tuofeichen/ME433-Advanced-Mechatronics/HW1/Clean 3.3 w: cap.png

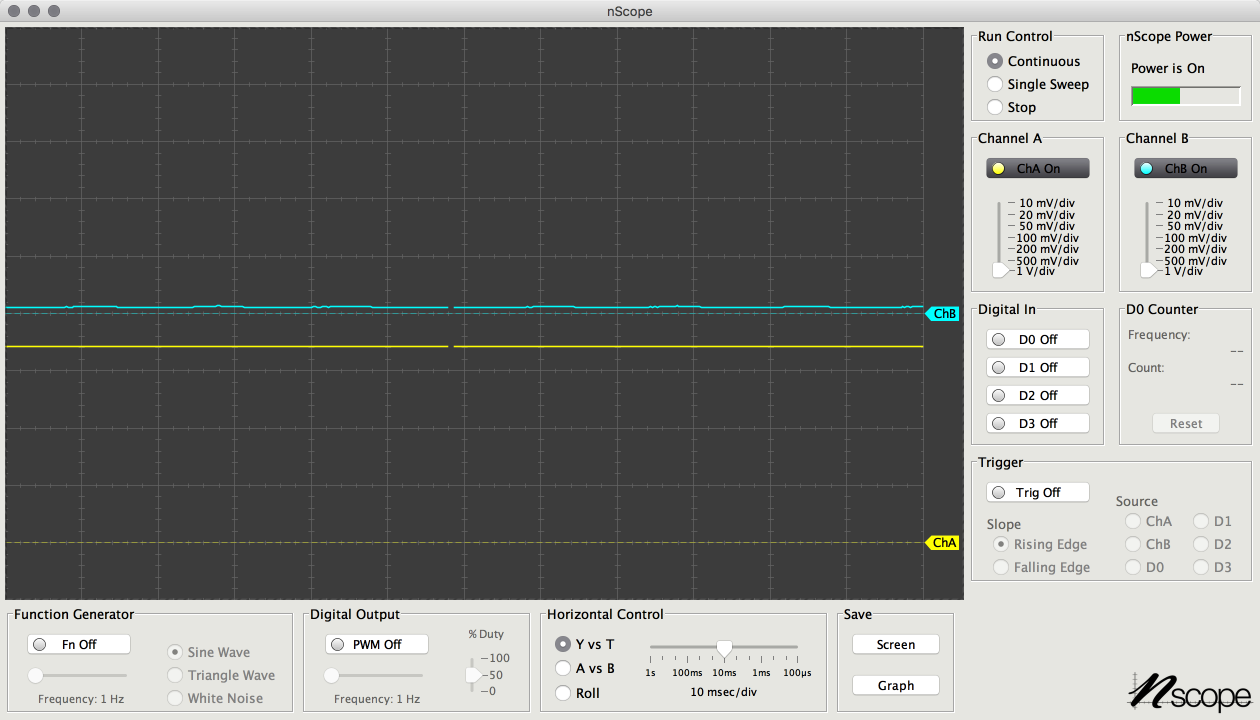
HW1/Clean 3.3 w: cap.png
