tuofeichen/ME433-Advanced-Mechatronics/HW1/HW1 Breadboard.jpg

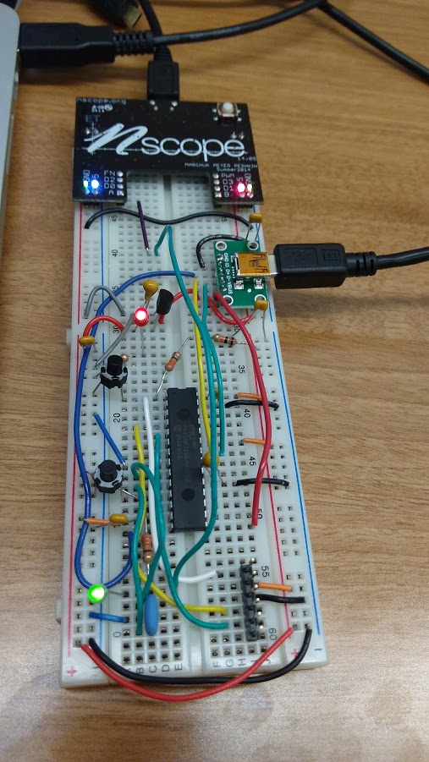
HW1/HW1 Breadboard.jpg
