tuofeichen/ME433-Advanced-Mechatronics/HW4/waveform.png

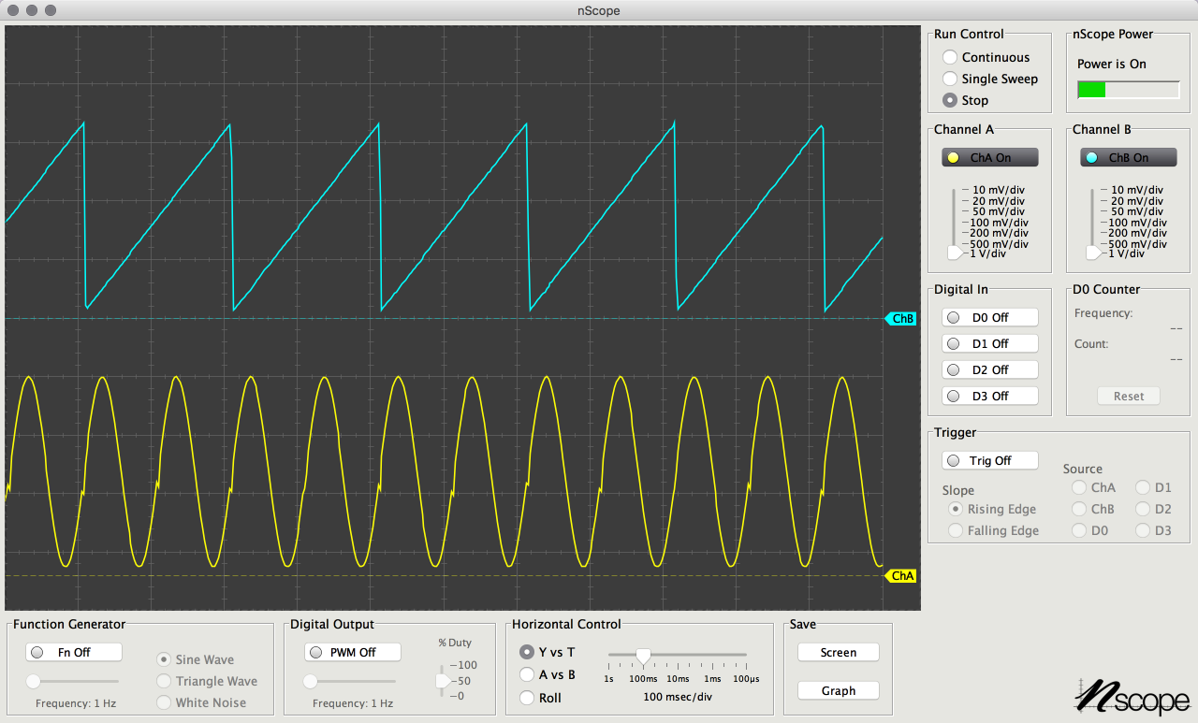
HW4/waveform.png
