tuofeichen/ME433-Advanced-Mechatronics/HW9/all_in_one6_mov.jpg

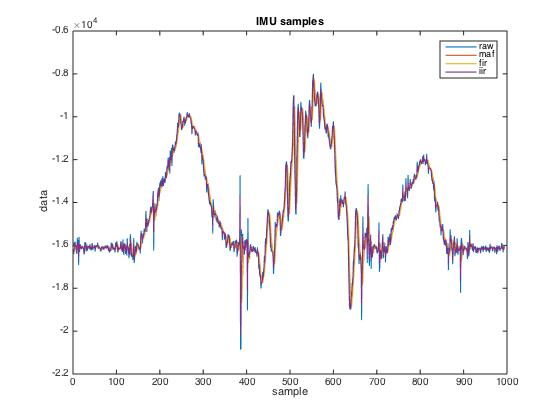
HW9/all_in_one6_mov.jpg
