tuofeichen/ME433-Advanced-Mechatronics/HW9/sep6_mov.jpg

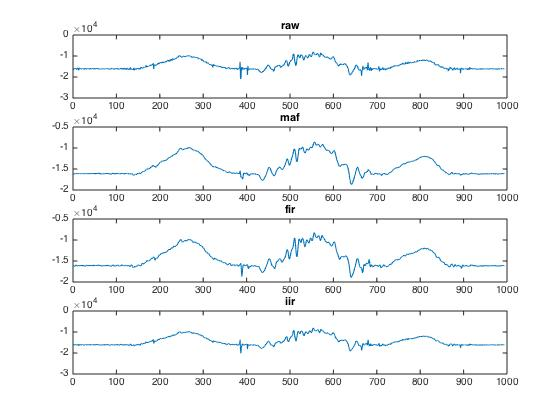
HW9/sep6_mov.jpg
