tuofeichen/ME433-Advanced-Mechatronics/HW17/box.jpg

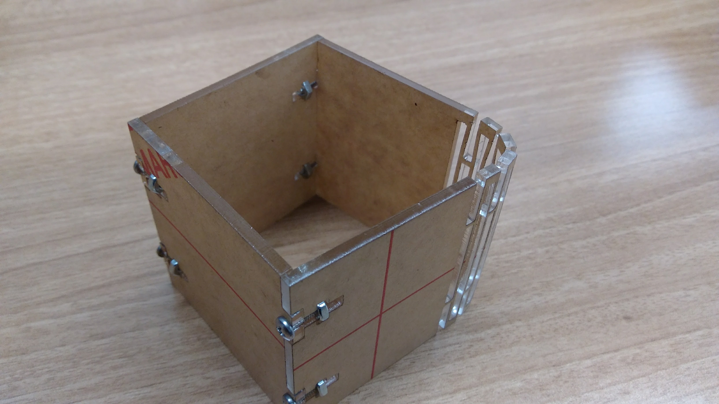
HW17/box.jpg
