tuofeichen/ME433-Advanced-Mechatronics/HW2/PIC_breakout_pcb/ME433.sch

## EAGLE design HW2/PIC_breakout_pcb/ME433.sch (2017-04-05)

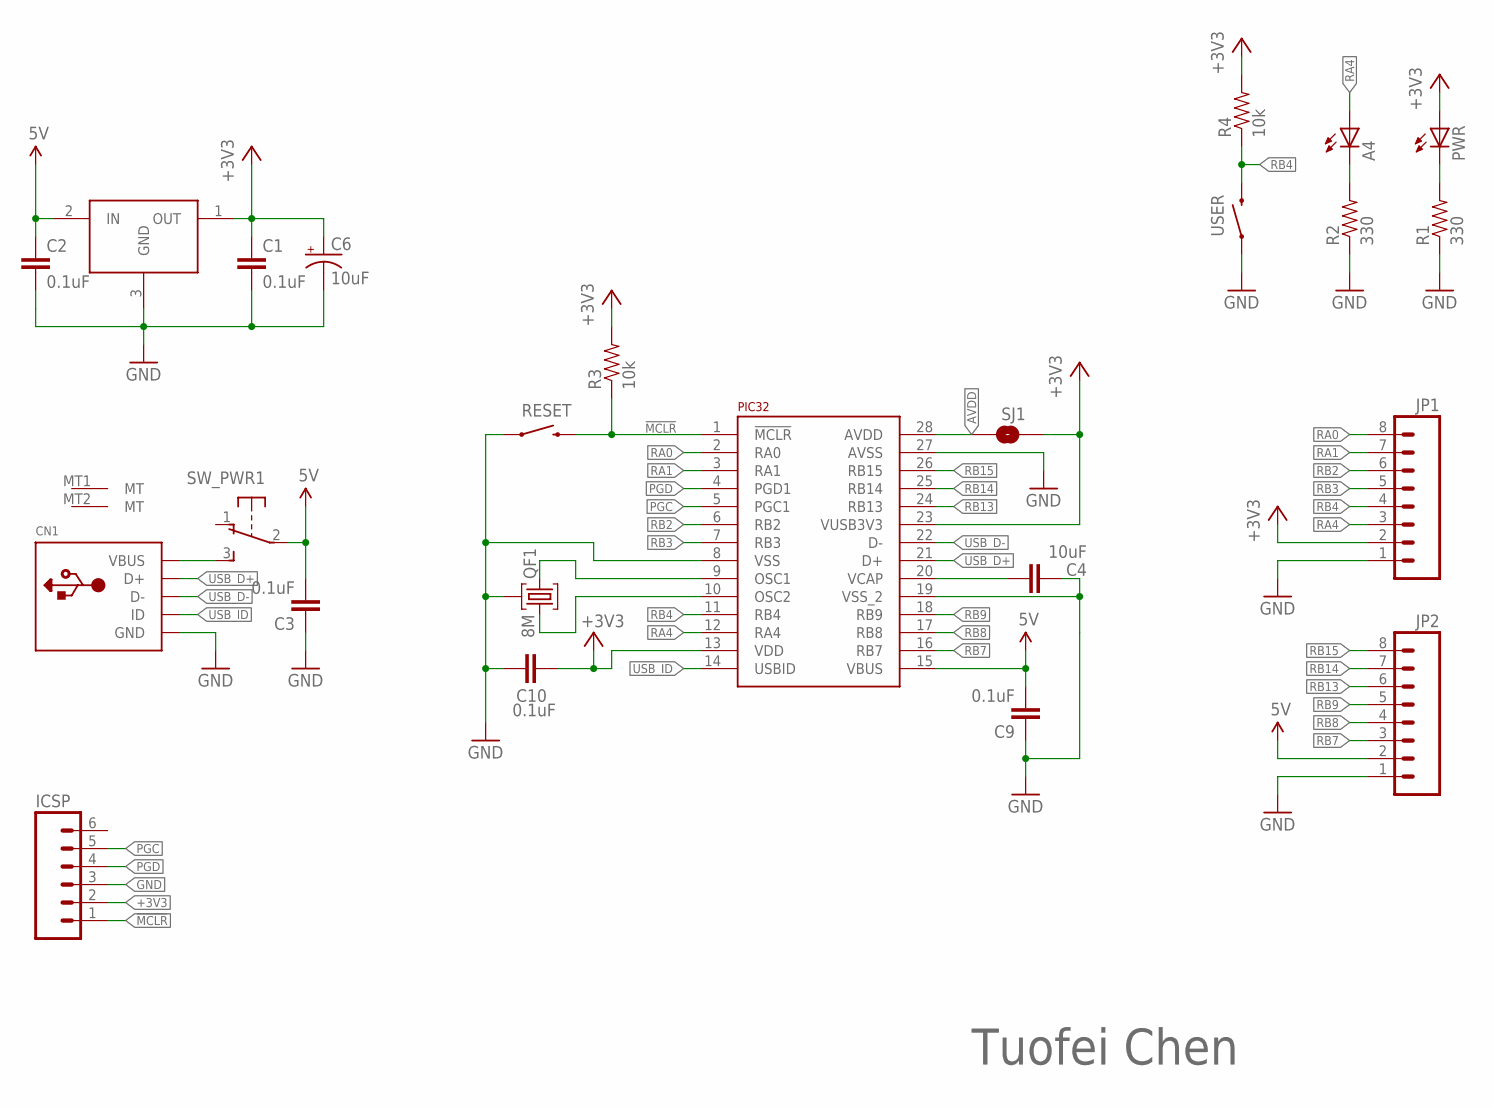
[picture p17: schematic ME433.sch]

Parts:
3V3-REG: 3V3-REG-TO92; TO-92
A4: LED3MM
C1, C2, C3, C9, C10: 0.1uF; CAP-PTH-SMALL
C4: 10uF; CAP-PTH-SMALL
C6: 10uF; CPOL-RADIAL-100UF-25V
CN1: USBMOLEX; USB-MINIB-THM-MOLEX
ICSP: M06LONGPADS; 1X06_LONGPADS
JP1, JP2: M08; 1X08
PIC32: PIC32MX250F128B-DIP; DIP28
PWR: LED3MM
QF1: 8M; HC49U
R1, R2: 330; AXIAL-0.3
R3, R4: 10k; AXIAL-0.3
RESET: PUSH_BUT; 1X02_LOCK_LONGPADS
SJ1: SOLDERJUMPERNC; SJ_2S
SW_PWR: EG1213
USER: PUSH_BUT; 1X02_LOCK_LONGPADS

Connections:
5V: 3V3-REG.2 (IN), C2.1, C3.2, C9.2, JP2.2, PIC32.15 (VBUS), SW_PWR.2
!MCLR: ICSP.1, PIC32.1 (!MCLR), R3.P$1 (1), RESET.2
+3V3: 3V3-REG.1 (OUT), C1.1, C6.1 (+), C10.2, ICSP.2, JP1.2, PIC32.13 (VDD), PIC32.23 (VUSB3V3), PWR.A, R3.P$2 (2), R4.P$2 (2), SJ1.1
AVDD: PIC32.28 (AVDD), SJ1.2
GND: 3V3-REG.3 (GND), C1.2, C2.2, C3.1, C4.2, C6.2 (-), C9.1, C10.1, CN1.GND, ICSP.3, JP1.1, JP2.1, PIC32.8 (VSS), PIC32.19 (VSS_2), PIC32.27 (AVSS), QF1.2, R1.P$1 (1), R2.P$1 (1), RESET.1, USER.1
unnamed: PIC32.9 (OSC1), QF1.1
unnamed: PIC32.10 (OSC2), QF1.3
unnamed: A4.K (C), R2.P$2 (2)
unnamed: C4.1, PIC32.20 (VCAP)
unnamed: PWR.K (C), R1.P$2 (2)
unnamed: CN1.VBUS, SW_PWR.3 (S)
PGC: ICSP.5, PIC32.5 (PGC1)
PGD: ICSP.4, PIC32.4 (PGD1)
RA0: JP1.8, PIC32.2 (RA0)
RA1: JP1.7, PIC32.3 (RA1)
RA4: A4.A, JP1.3, PIC32.12 (RA4)
RB2: JP1.6, PIC32.6 (RB2)
RB3: JP1.5, PIC32.7 (RB3)
RB4: JP1.4, PIC32.11 (RB4), R4.P$1 (1), USER.2
RB7: JP2.3, PIC32.16 (RB7)
RB8: JP2.4, PIC32.17 (RB8)
RB9: JP2.5, PIC32.18 (RB9)
RB13: JP2.6, PIC32.24 (RB13)
RB14: JP2.7, PIC32.25 (RB14)
RB15: JP2.8, PIC32.26 (RB15)
USB_D+: CN1.D+, PIC32.21 (D+)
USB_D-: CN1.D-, PIC32.22 (D-)
USB_ID: CN1.ID, PIC32.14 (USBID)

Notes on the sheet:
Tuofei Chen
