tuofeichen/ME433-Advanced-Mechatronics/HW11/firmware/src/i2c.c

#include "i2c.h"


// I2C Master utilities, 100 kHz, using polling rather than interrupts
// The functions must be callled in the correct order as per the I2C protocol
// Change I2C2 to the I2C channel you are using
// I2C pins need pull-up resistors, 2k-10k

void i2c_master_init(void) {
  I2C2BRG = 233; //some number for 100kHz;              // I2CBRG = [1/(2*Fsck) - PGD]*Pblck - 2                                           // look up PGD for your PIC32
  ANSELBbits.ANSB2 = 0;                                 // turn off analog pin function for sda2
  ANSELBbits.ANSB3 = 0;                                 // turn off analog pin function for scl2
  I2C2CONbits.ON = 1;                                   // turn on the I2C2 module
}

// Start a transmission on the I2C bus
void i2c_master_start(void) {
    I2C2CONbits.SEN = 1;            // send the start bit
    while(I2C2CONbits.SEN) { ; }    // wait for the start bit to be sent
}

void i2c_master_restart(void) {     
    I2C2CONbits.RSEN = 1;           // send a restart 
    while(I2C2CONbits.RSEN) { ; }   // wait for the restart to clear
}

void i2c_master_send(unsigned char byte) { // send a byte to slave
  I2C2TRN = byte;                   // if an address, bit 0 = 0 for write, 1 for read
  while(I2C2STATbits.TRSTAT) { ; }  // wait for the transmission to finish
  
  if(I2C2STATbits.ACKSTAT) {        // if this is high, slave has not acknowledged
     PORTAINV = 0x0010; // turn on green led
      // ("I2C2 Master: failed to receive ACK\r\n");
  }
}

unsigned char i2c_master_recv(void) { // receive a byte from the slave
    I2C2CONbits.RCEN = 1;             // start receiving data
    while(!I2C2STATbits.RBF) { ; }    // wait to receive the data
    return I2C2RCV;                   // read and return the data
}

void i2c_master_ack(int val) {        // sends ACK = 0 (slave should send another byte)
                                      // or NACK = 1 (no more bytes requested from slave)
    I2C2CONbits.ACKDT = val;          // store ACK/NACK in ACKDT
    I2C2CONbits.ACKEN = 1;            // send ACKDT
    while(I2C2CONbits.ACKEN) { ; }    // wait for ACK/NACK to be sent
}

void i2c_master_stop(void) {          // send a STOP:
  I2C2CONbits.PEN = 1;                // comm is complete and master relinquishes bus
  while(I2C2CONbits.PEN) { ; }        // wait for STOP to complete
}

void i2c_expander_init()
{
    i2c_master_start();
    i2c_master_send(SLAVE_ADDR << 1);
    i2c_master_send(0x00); // write to IODIR
    i2c_master_send(0x80); // 7 is input, 0 is output
    i2c_master_stop();
    
    
    i2c_master_start();
    i2c_master_send(SLAVE_ADDR << 1 );
    i2c_master_send(0x05); // write to IOCON
    i2c_master_send(0x30); // 7 is input, 0 is output 0b00110000 disable sequential read
    i2c_master_stop();
    
    i2c_master_start();
    i2c_master_send(SLAVE_ADDR << 1 );
    i2c_master_send(0x06); // write to IODIR
    i2c_master_send(0x80); // 7 is pull up resistor
    i2c_master_stop();
    
}

char i2c_expander_detect()
{
    char c = 0;
    i2c_master_start();
    i2c_master_send(SLAVE_ADDR << 1);
    i2c_master_send(0x09); // read gpio register port 
    i2c_master_restart();
    i2c_master_send((SLAVE_ADDR << 1)|1);
    c = i2c_master_recv();
    i2c_master_ack(1);
    i2c_master_stop();
    return c; 
}

void i2c_expander_write(char pin, char on)
{
    char c = i2c_expander_detect(); 
    
    char data;
    
    if (on){
        data  = on << pin;   
        c |= data; 
    }
    else
    {
        data = 0xff;
        data ^= (1 << pin);
        c &= data; 
    }
    
    i2c_master_start();
    i2c_master_send(SLAVE_ADDR << 1);
    i2c_master_send(0x09); // write to PORT
    i2c_master_send(c);    // turn on bit
    i2c_master_stop();
}
