tuofeichen/ME433-Advanced-Mechatronics/HW18/firmware/src/vive.h

#ifndef _VIVE_H    /* Guard against multiple inclusion */
#define _VIVE_H
#include "app.h"
#include <xc.h>

void vive_init();


#endif /* _EXAMPLE_FILE_NAME_H */

/* *****************************************************************************
 End of File
 */
