tuofeichen/ME433-Advanced-Mechatronics/HW11/firmware/src/imu.h

#ifndef _IMU_H    /* Guard against multiple inclusion */
#define _IMU_H

#include "i2c.h"
#include "tft.h"
#include "app.h"

#define     IMU_ADDR   0b1101010 // chosen hardware bit 0
#define     IMU_RES    32768; // 2 to the 15th power for each direction
enum regAddr
{
      FUNC_CFG_ACCESS   = 0x01,

      FIFO_CTRL1        = 0x06,
      FIFO_CTRL2        = 0x07,
      FIFO_CTRL3        = 0x08,
      FIFO_CTRL4        = 0x09,
      FIFO_CTRL5        = 0x0A,
      ORIENT_CFG_G      = 0x0B,

      INT1_CTRL         = 0x0D,
      INT2_CTRL         = 0x0E,
      WHO_AM_I          = 0x0F,
      CTRL1_XL          = 0x10,
      CTRL2_G           = 0x11,
      CTRL3_C           = 0x12,
      CTRL4_C           = 0x13,
      CTRL5_C           = 0x14,
      CTRL6_C           = 0x15,
      CTRL7_G           = 0x16,
      CTRL8_XL          = 0x17,
      CTRL9_XL          = 0x18,
      CTRL10_C          = 0x19,

      WAKE_UP_SRC       = 0x1B,
      TAP_SRC           = 0x1C,
      D6D_SRC           = 0x1D,
      STATUS_REG        = 0x1E,

      OUT_TEMP_L        = 0x20,
      OUT_TEMP_H        = 0x21,
      OUTX_L_G          = 0x22,
      OUTX_H_G          = 0x23,
      OUTY_L_G          = 0x24,
      OUTY_H_G          = 0x25,
      OUTZ_L_G          = 0x26,
      OUTZ_H_G          = 0x27,
      OUTX_L_XL         = 0x28,
      OUTX_H_XL         = 0x29,
      OUTY_L_XL         = 0x2A,
      OUTY_H_XL         = 0x2B,
      OUTZ_L_XL         = 0x2C,
      OUTZ_H_XL         = 0x2D,

      FIFO_STATUS1      = 0x3A,
      FIFO_STATUS2      = 0x3B,
      FIFO_STATUS3      = 0x3C,
      FIFO_STATUS4      = 0x3D,
      FIFO_DATA_OUT_L   = 0x3E,
      FIFO_DATA_OUT_H   = 0x3F,
      TIMESTAMP0_REG    = 0x40,
      TIMESTAMP1_REG    = 0x41,
      TIMESTAMP2_REG    = 0x42,

      STEP_TIMESTAMP_L  = 0x49,
      STEP_TIMESTAMP_H  = 0x4A,
      STEP_COUNTER_L    = 0x4B,
      STEP_COUNTER_H    = 0x4C,

      FUNC_SRC          = 0x53,

      TAP_CFG           = 0x58,
      TAP_THS_6D        = 0x59,
      INT_DUR2          = 0x5A,
      WAKE_UP_THS       = 0x5B,
      WAKE_UP_DUR       = 0x5C,
      FREE_FALL         = 0x5D,
      MD1_CFG           = 0x5E,
      MD2_CFG           = 0x5F,
 };



void imu_init();
void imu_test(); // read who am i, if correct draw green bar/ else draw red bar

uint8_t imu_read (uint8_t reg);
void imu_read_seq (uint8_t reg, uint8_t len, uint8_t* out);
void imu_write(uint8_t reg, uint8_t value);

void imu_read_gyro(int16_t* gyro);
void imu_read_acc (int16_t* acc);



#endif /* _EXAMPLE_FILE_NAME_H */

/* *****************************************************************************
 End of File
 */
