tuofeichen/ME433-Advanced-Mechatronics/HW11/firmware/src/i2c.h

#ifndef _I2C_H
#define _I2C_H
#include<xc.h>  
#include<sys/attribs.h>  // __ISR macro

#define     SLAVE_ADDR 0b0100000 // hardware address 000 for i2c expander



// Header file for i2c_master_noint.c
// helps implement use I2C1 as a master without using interrupts

void i2c_master_init(void);              // set up I2C2 as a master, at 100 kHz

void i2c_master_start(void);              // send a START signal
void i2c_master_restart(void);            // send a RESTART signal
void i2c_master_send(unsigned char byte); // send a byte (either an address or data)
unsigned char i2c_master_recv(void);      // receive a byte of data
void i2c_master_ack(int val);             // send an ACK (0) or NACK (1)
void i2c_master_stop(void);               // send a stop

void i2c_expander_init(void);
void i2c_expander_write(char pin, char on);

#endif
